jreahl/LMI-Lidar-Mapping-Instrument/LMI_mount_SolidWorks/LIDAR_mount_base.SLDPRT

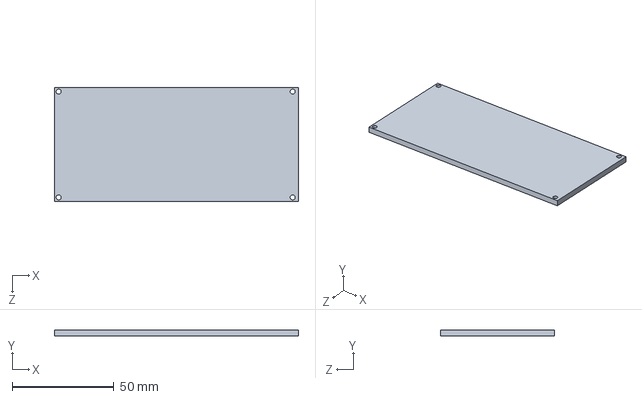
[picture p27: CAD file, 2018-05-21]
LMI_mount_SolidWorks/LIDAR_mount_base.SLDPRT
119.8 x 2.95 x 55.9 mm
