jreahl/LMI-Lidar-Mapping-Instrument/LMI_mount_SolidWorks/LIDAR_mount_LIDAR_mount.SLDPRT

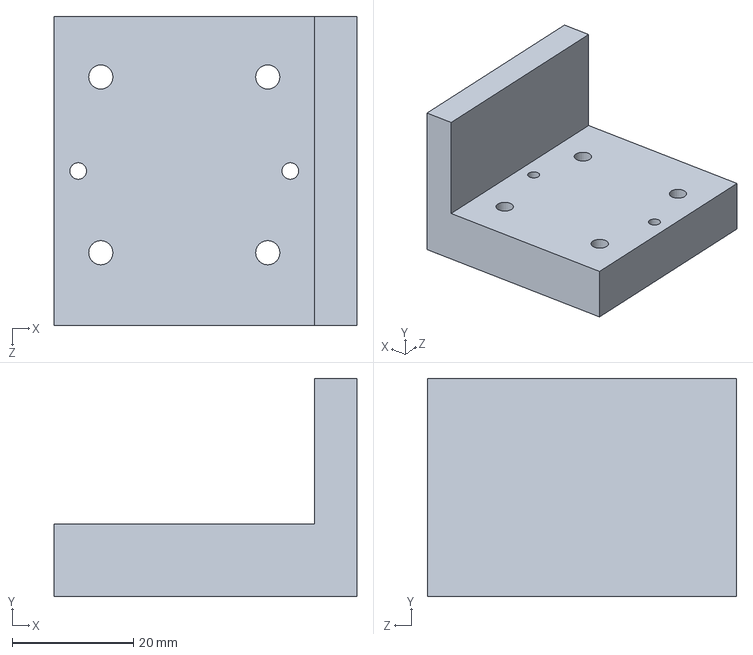
[picture p28: CAD file, 2018-05-21]
LMI_mount_SolidWorks/LIDAR_mount_LIDAR_mount.SLDPRT
50.0 x 36.0 x 51.0 mm
