jreahl/LMI-Lidar-Mapping-Instrument/LMI_mount_SolidWorks/LIDAR_wirefeed.SLDPRT

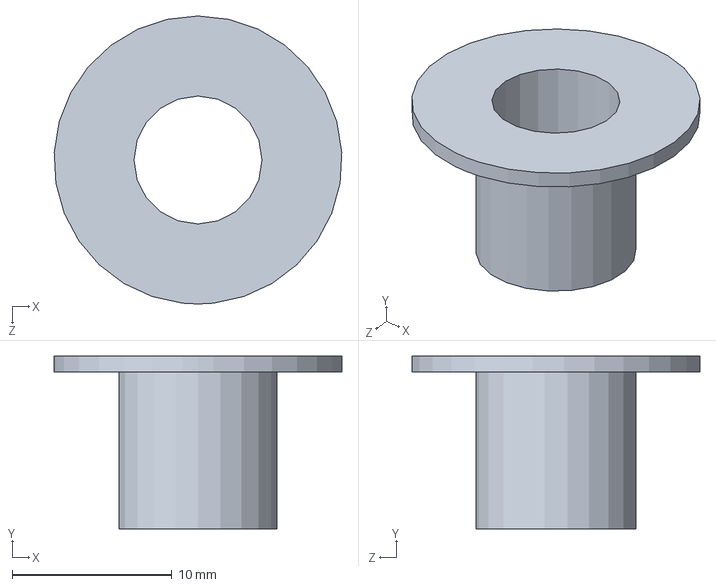
[picture p29: CAD file, 2018-05-21]
LMI_mount_SolidWorks/LIDAR_wirefeed.SLDPRT
18.0 x 10.8 x 18.0 mm
