jreahl/LMI-Lidar-Mapping-Instrument/plot-lidar-cloud/test2_filtered.csv

x | y | z
94 | 0 | 0
93 | 0 | 1
93 | 0 | 3
93 | 0 | 4
94 | 0 | 6
110 | 0 | 9
119 | 0 | 12
119 | 0 | 14
120 | 0 | 16
91 | 0 | 14
92 | 0 | 16
93 | 0 | 18
146 | 0 | 31
240 | 0 | 55
278 | 0 | 69
357 | 0 | 95
434 | 0 | 124
458 | 0 | 140
480 | 0 | 156
540 | 0 | 186
599 | 0 | 218
594 | 0 | 228
453 | 0 | 183
447 | 0 | 189
447 | 0 | 199
4 | 0 | 2
506 | 8 | 225
459 | 8 | 194
451 | 7 | 182
451 | 7 | 173
538 | 9 | 195
607 | 10 | 209
553 | 9 | 179
530 | 9 | 162
483 | 8 | 138
472 | 8 | 126
450 | 7 | 112
370 | 6 | 85
264 | 4 | 56
239 | 4 | 46
221 | 3 | 39
197 | 3 | 31
184 | 3 | 25
170 | 2 | 20
160 | 2 | 16
149 | 2 | 13
140 | 2 | 9
130 | 2 | 6
121 | 2 | 4
113 | 1 | 1
117 | 2 | 0
109 | 3 | 0
107 | 3 | 1
107 | 3 | 3
107 | 3 | 5
106 | 3 | 7
106 | 3 | 9
120 | 4 | 12
141 | 4 | 17
141 | 4 | 19
173 | 6 | 27
174 | 6 | 30
215 | 7 | 41
216 | 7 | 45
244 | 8 | 56
270 | 9 | 67
403 | 14 | 108
433 | 15 | 124
460 | 16 | 140
517 | 18 | 168
552 | 19 | 190
845 | 29 | 324
467 | 16 | 188
448 | 15 | 190
459 | 16 | 204
4 | 0 | 2
2119 | 111 | 944
550 | 28 | 234
458 | 24 | 185
483 | 25 | 185
573 | 30 | 208
879 | 46 | 303
561 | 29 | 182
537 | 28 | 164
538 | 28 | 154
502 | 26 | 134
449 | 23 | 112
366 | 19 | 84
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
