jreahl/LMI-Lidar-Mapping-Instrument/plot-lidar-cloud/test3_filtered.csv

x | y | z
107 | 0 | 0
105 | 0 | 1
107 | 0 | 3
107 | 0 | 5
105 | 0 | 7
122 | 0 | 10
130 | 0 | 13
137 | 0 | 16
145 | 0 | 20
169 | 0 | 26
189 | 0 | 33
208 | 0 | 40
208 | 0 | 44
270 | 0 | 62
271 | 0 | 67
406 | 0 | 108
440 | 0 | 126
470 | 0 | 143
501 | 0 | 162
547 | 0 | 188
862 | 0 | 313
858 | 0 | 329
463 | 0 | 187
449 | 0 | 190
471 | 0 | 209
458 | 8 | 194
450 | 7 | 182
452 | 7 | 173
459 | 8 | 167
875 | 15 | 301
565 | 9 | 183
543 | 9 | 166
495 | 8 | 142
476 | 8 | 127
446 | 7 | 111
369 | 6 | 85
265 | 4 | 56
245 | 4 | 47
219 | 3 | 38
196 | 3 | 31
187 | 3 | 26
170 | 2 | 20
157 | 2 | 16
142 | 2 | 12
141 | 2 | 9
129 | 2 | 6
121 | 2 | 4
114 | 2 | 2
109 | 1 | 0
108 | 3 | 0
108 | 3 | 1
108 | 3 | 3
108 | 3 | 5
108 | 3 | 7
108 | 3 | 9
125 | 4 | 13
139 | 4 | 17
160 | 5 | 22
160 | 5 | 25
181 | 6 | 31
202 | 7 | 39
218 | 7 | 46
250 | 8 | 57
266 | 9 | 66
433 | 15 | 116
463 | 16 | 132
489 | 17 | 149
539 | 18 | 175
568 | 19 | 195
879 | 30 | 320
864 | 30 | 332
453 | 15 | 183
448 | 15 | 190
447 | 15 | 199
547 | 28 | 232
458 | 24 | 185
479 | 25 | 184
572 | 29 | 208
879 | 46 | 303
588 | 30 | 191
540 | 28 | 165
540 | 28 | 155
522 | 27 | 140
438 | 23 | 109
378 | 19 | 87
272 | 14 | 58
244 | 12 | 47
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
