jreahl/LMI-Lidar-Mapping-Instrument/LMI_Code/Grassin_C_code/LidarViewer/LidarViewer.pde

// LidarViewer.pde Processing sketch
// http://www.charleslabs.fr/en/project-3D+Lidar+Scanner

// Load sketch into Processing, available from:
// https://processing.org/
// You also need to install the PeasyCam library.

// This software read coordinates of the Arduino Lidar 
// (format: "X Y Z") and displays it as a 3D point cloud that you
// can move around using the mouse.
// Press 's' to save the cloud as a text file in Processing directory.

import processing.serial.*;
import peasy.*;
import java.io.FileWriter;
import java.util.Calendar;
import java.text.SimpleDateFormat;

Serial serial;
PeasyCam cam;
int serialPortNumber = 1;
final float angleIncrement=0.1f;

ArrayList<PVector> pointList;

void setup() {
  size(800, 640, P3D);
  colorMode(RGB, 255, 255, 255);
  pointList = new ArrayList<PVector>();
  
  // PeasyCam
  cam = new PeasyCam(this, 800);
  cam.rotateZ(-3.1415/4);
  cam.rotateX(-3.1415/4);
  
  // Serial Port
  try{
    String[] serialPorts = Serial.list();
    println("Serial ports:");
    printArray(serialPorts);
    println("Selected: ["+serialPortNumber+"]");
    String serialPort = serialPorts[serialPortNumber];
    println("Using serial port \"" + serialPort + "\"");
 
    serial = new Serial(this, serialPort, 115200);
  } catch(Exception e){
    println("Not able to connect to serialPort (error:"+e.getClass().getName()+")");
    exit();
  }
}

void draw() {
  // Prepare window & drawing
  perspective();
  background(33);
  stroke(255,255,255);
  sphere(0.5f);
  fill(50);
  ellipse(0, 0, 10, 10);

  //Read Serial Port (if we can)
  String serialString = serial.readStringUntil('\n');
  if (serialString != null) {
    String[] coordinates = split(serialString, ' ');
    if (coordinates.length == 3) {
      pointList.add(new PVector(float(coordinates[0]), float(coordinates[1]), float(coordinates[2])));
    }
  }
 
  // Draw the actual point cloud
  for (int index = 0; index < pointList.size(); index++) {
    PVector v = pointList.get(index);
    if (index == pointList.size() - 1) {
      // Draw a line between Lidar and last point
      stroke(255, 15, 15);
      line(0, 0, 0, v.x,v.y,v.z);
    }
    // Draw point with a variable color
    stroke(255-v.z, 255-v.y, 255-v.x);
    point(v.x, v.y, v.z);
  }
}

// Handle keyboard events : movement, save & clear all points.
void keyReleased() {
  if (key =='x') {
    // erase all points
    pointList.clear();
  } else if(key == 's'){
    saveToFile();
  }
  else if (key == CODED) {
    if (keyCode == UP) {
      cam.rotateX(angleIncrement);
    } else if (keyCode == DOWN) {
      cam.rotateX(-angleIncrement);
    }else if (keyCode == LEFT) {
      cam.rotateY(angleIncrement);
    }else if (keyCode == RIGHT) {
      cam.rotateY(-angleIncrement);
    }
  }
}

// Function to save the point cloud in the Processing install directory
void saveToFile(){
  String fileName = "./points_"+
        new SimpleDateFormat("yyMMdd_HHmmss").format(Calendar.getInstance().getTime())+".xyz";
  PrintWriter pw = null;
 
  try{
    pw = new PrintWriter(new FileWriter(fileName,true));
    for(int i=0;i<pointList.size();i++)
      pw.println((int)pointList.get(i).x + " " + 
                  (int)pointList.get(i).y + " " +
                  (int)pointList.get(i).z);
  }
  catch(Exception e){
  }
  finally {
    if(pw != null) pw.close();
  }
}
